Conexiotechnologies/conexio-stratus-board-schematics/conexio-stratus-nRF9160-shield/images/Stratus Shield Bottom.png

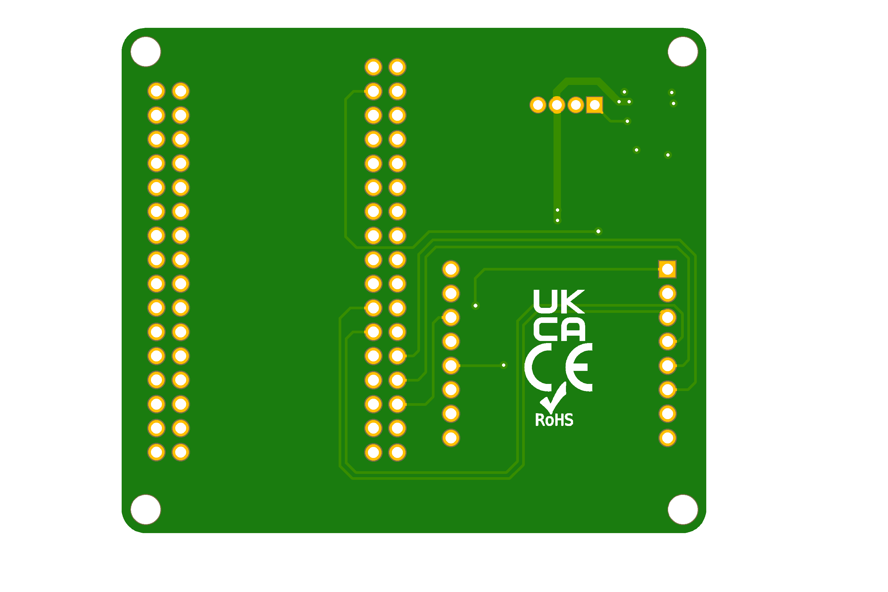
conexio-stratus-nRF9160-shield/images/Stratus Shield Bottom.png
