Conexiotechnologies/conexio-stratus-board-schematics/conexio-stratus-nRF9160-shield/images/Stratus Shield Top.png

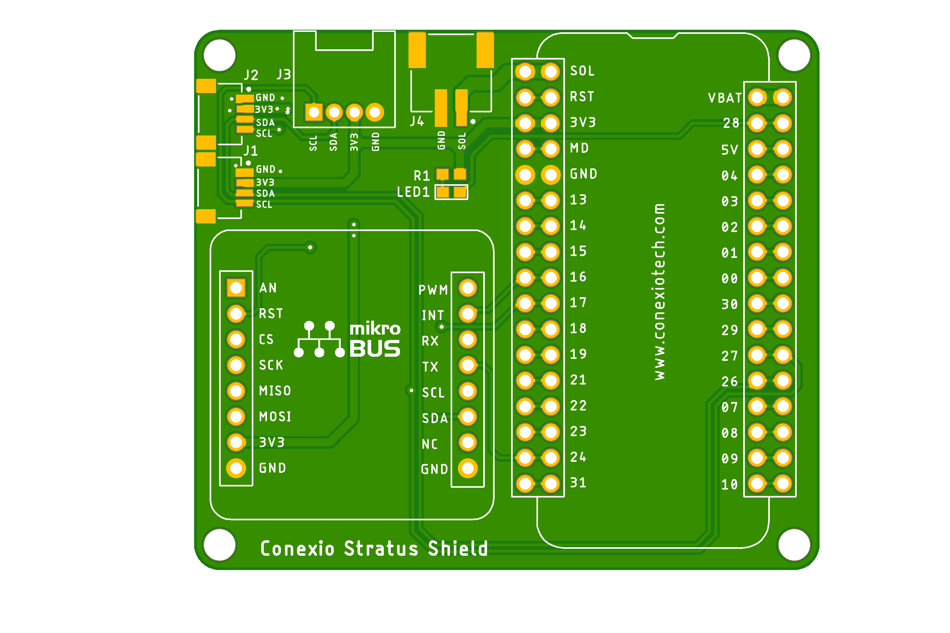
conexio-stratus-nRF9160-shield/images/Stratus Shield Top.png
