Conexiotechnologies/conexio-stratus-board-schematics/conexio-stratus-nRF9160/images/bottom.png

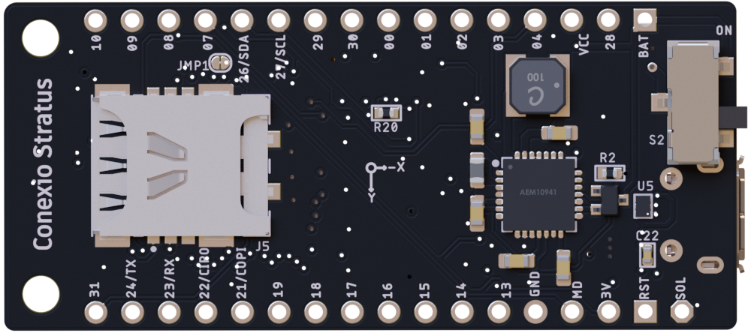
conexio-stratus-nRF9160/images/bottom.png
