Conexiotechnologies/conexio-stratus-board-schematics/conexio-stratus-nRF9160/images/stratus-shield.png

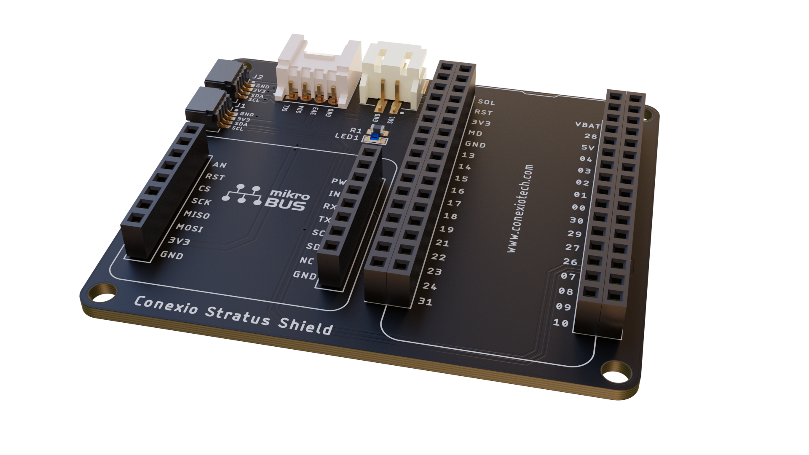
conexio-stratus-nRF9160/images/stratus-shield.png
