Conexiotechnologies/conexio-stratus-board-schematics/conexio-stratus-nRF9160/images/stratus_plus_shield.png

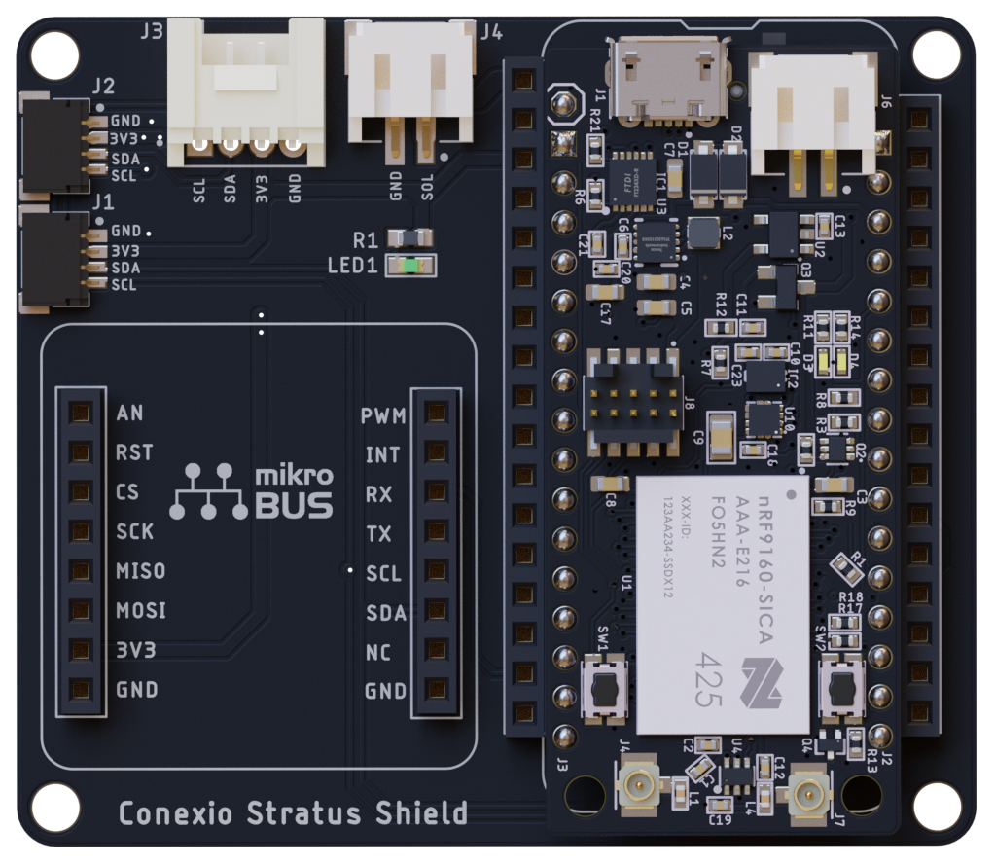
conexio-stratus-nRF9160/images/stratus_plus_shield.png
