Conexiotechnologies/conexio-stratus-board-schematics/conexio-stratus-nRF9160/Stratus-nRF9160-PCB/Pictures/stratus-nRF9160_Bottom.png

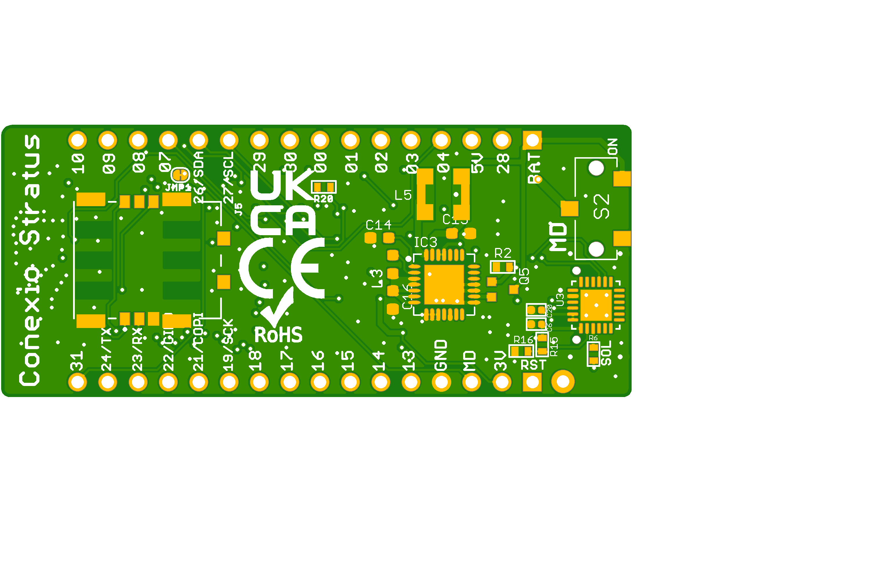
conexio-stratus-nRF9160/Stratus-nRF9160-PCB/Pictures/stratus-nRF9160_Bottom.png
