Conexiotechnologies/conexio-stratus-board-schematics/conexio-stratus-nRF9160/Stratus-nRF9160-PCB/Pictures/stratus-nRF9160_Top.png

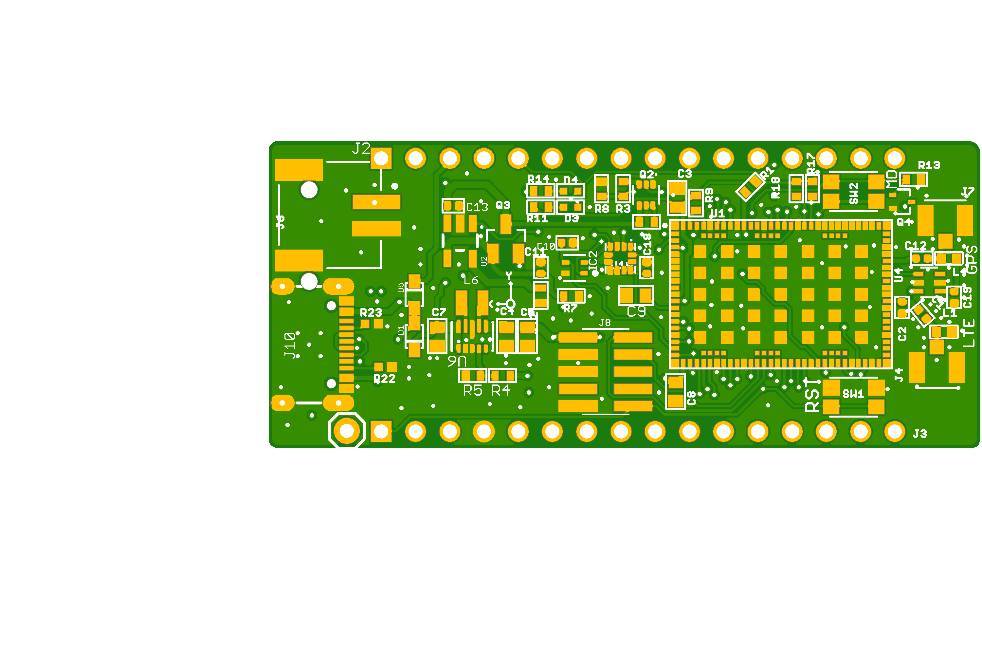
conexio-stratus-nRF9160/Stratus-nRF9160-PCB/Pictures/stratus-nRF9160_Top.png
