Conexiotechnologies/conexio-stratus-board-schematics/conexio-stratus-pro-nRF9151-V1.4/Images/2D Bottom.png

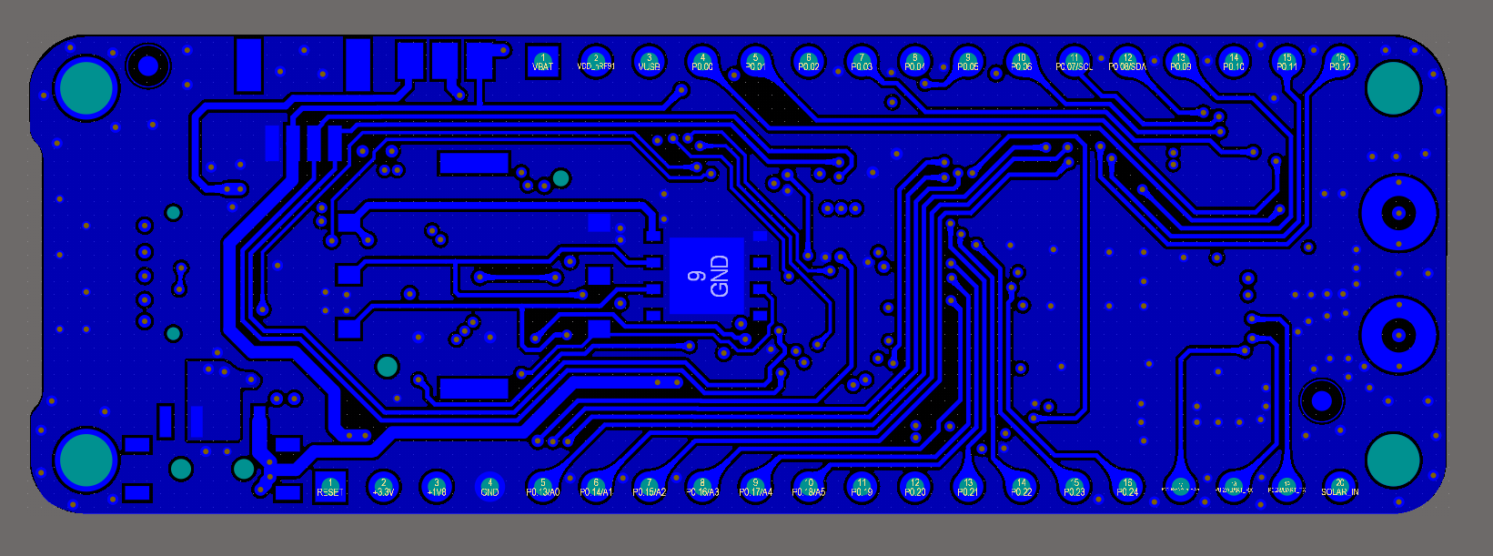
conexio-stratus-pro-nRF9151-V1.4/Images/2D Bottom.png
