Conexiotechnologies/conexio-stratus-board-schematics/conexio-stratus-pro-nRF9151-V1.4/Images/Mid 1 2D.jpg

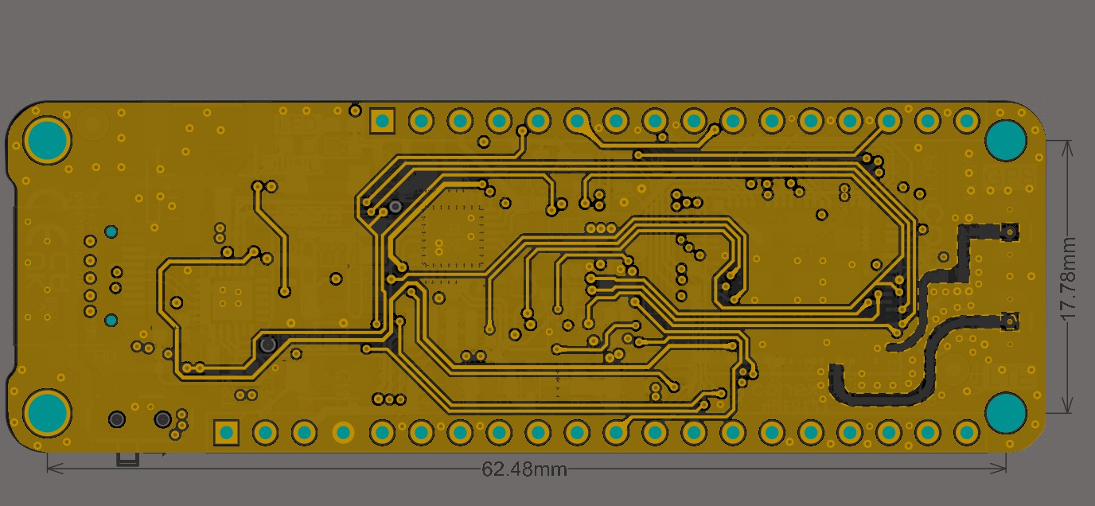
conexio-stratus-pro-nRF9151-V1.4/Images/Mid 1 2D.jpg
