Conexiotechnologies/conexio-stratus-board-schematics/conexio-stratus-pro-nRF9151-V1.4/Images/Top 2D.jpg

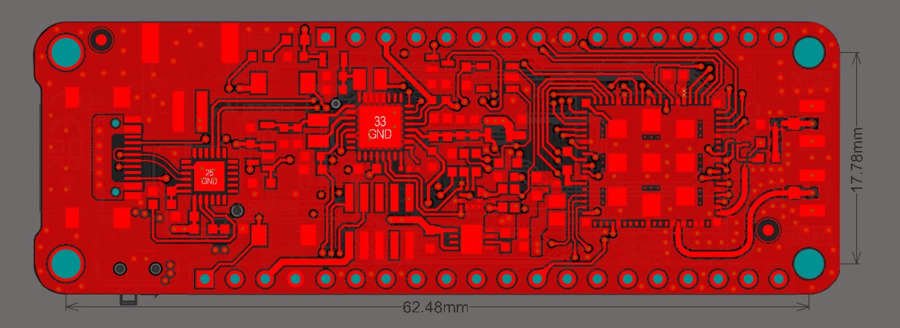
conexio-stratus-pro-nRF9151-V1.4/Images/Top 2D.jpg
