Conexiotechnologies/conexio-stratus-board-schematics/conexio-stratus-pro-nRF9161/images/stratus-pro-nRF9161-breadboard.png

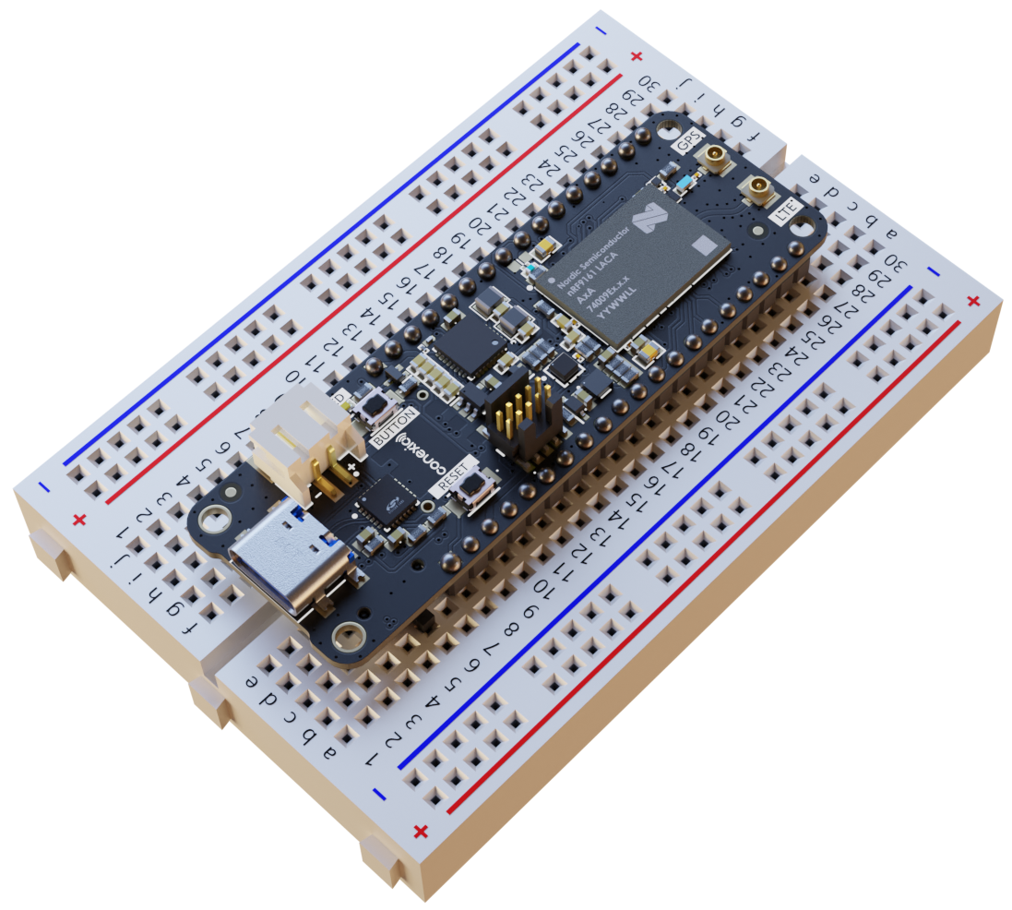
conexio-stratus-pro-nRF9161/images/stratus-pro-nRF9161-breadboard.png
