Conexiotechnologies/conexio-stratus-board-schematics/stratus-pro-expansion-dock/Images/2D Bottom.jpg

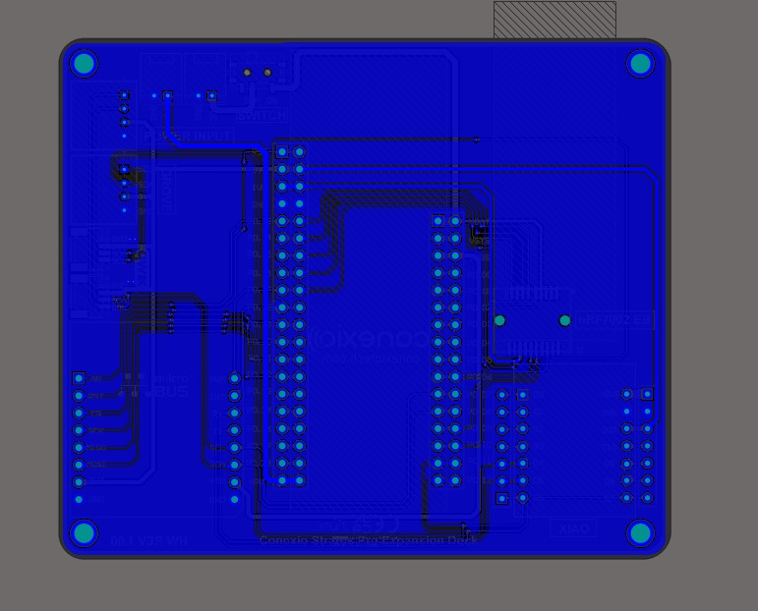
stratus-pro-expansion-dock/Images/2D Bottom.jpg
