Conexiotechnologies/conexio-stratus-board-schematics/stratus-pro-expansion-dock/Images/3d bottom img.png

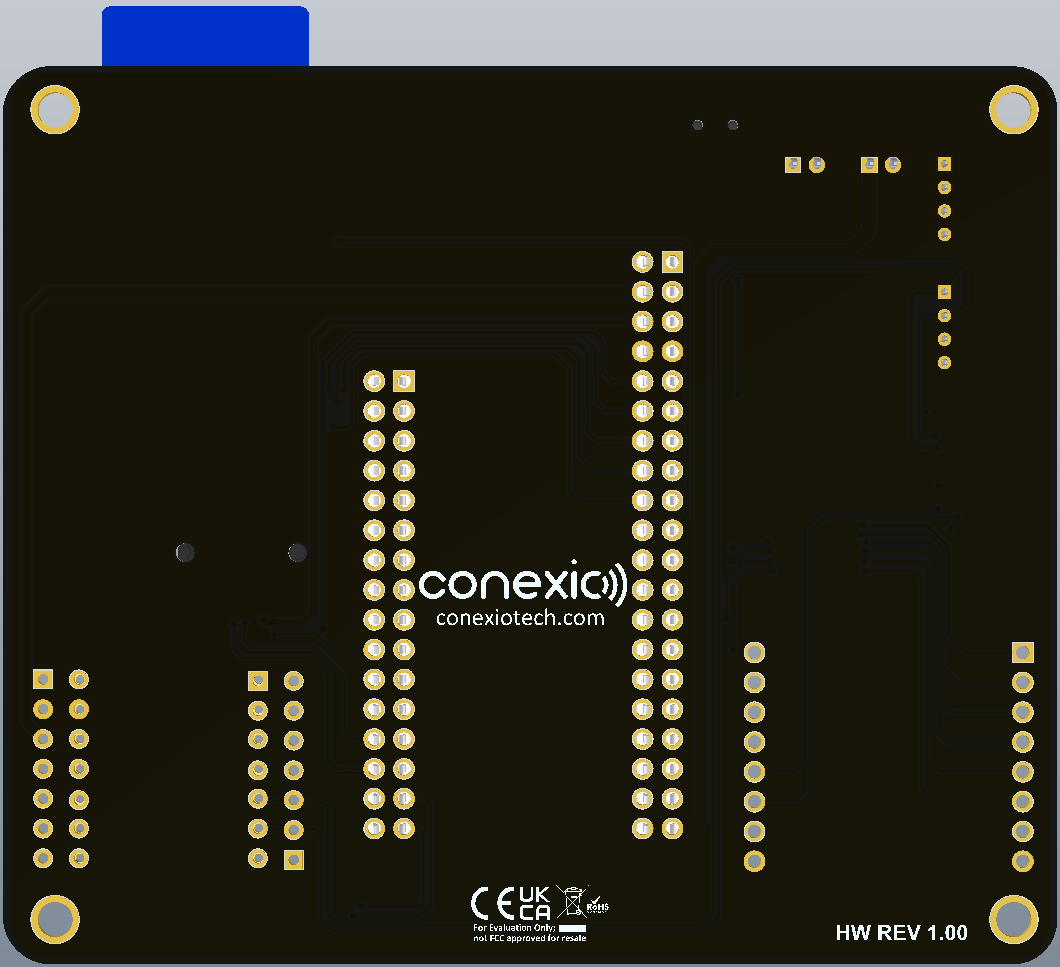
stratus-pro-expansion-dock/Images/3d bottom img.png
