Conexiotechnologies/conexio-stratus-board-schematics/stratus-pro-expansion-dock/Images/3d top img.png

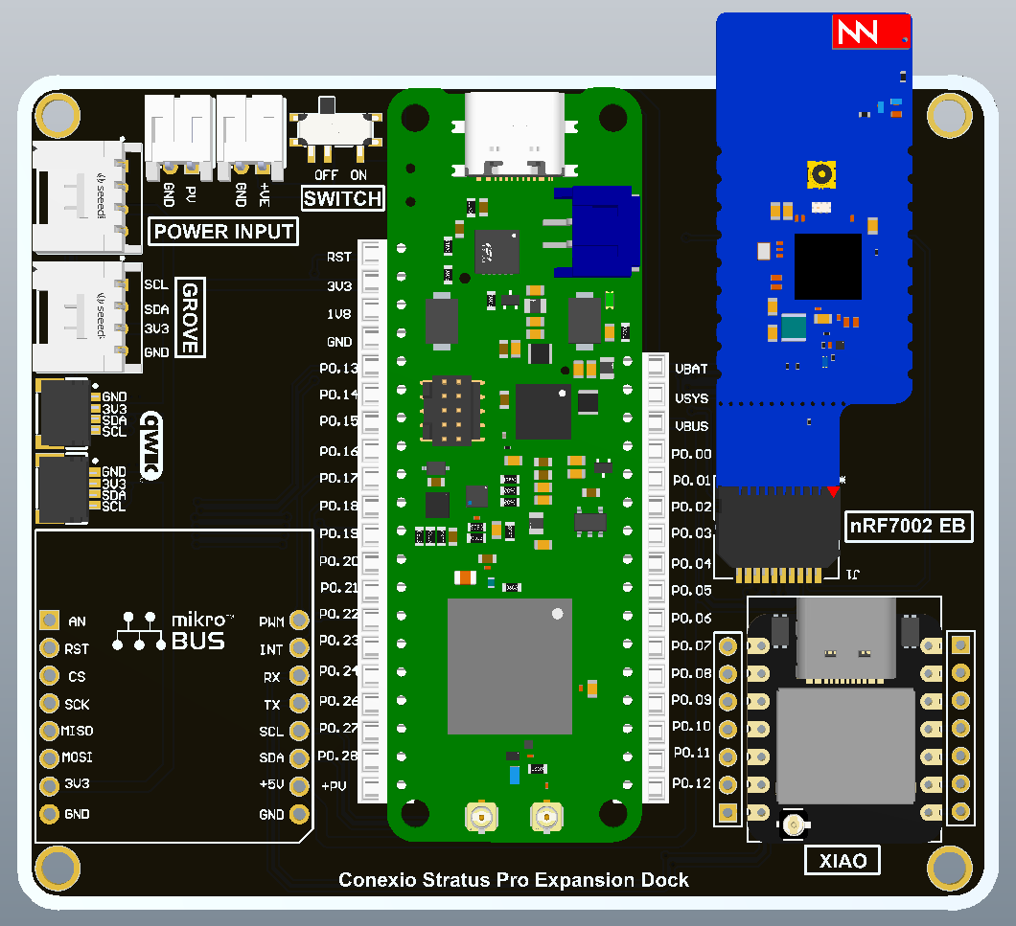
stratus-pro-expansion-dock/Images/3d top img.png
