Conexiotechnologies/conexio-stratus-board-schematics/stratus-pro-expansion-dock/Images/expansion dock populated.png

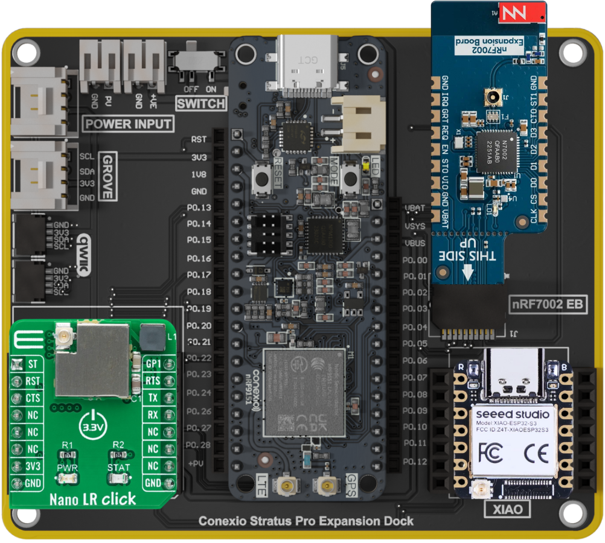
stratus-pro-expansion-dock/Images/expansion dock populated.png
